lllllcf/APMC-STPM-for-SCR/figure-data/houlai/formatlab.png

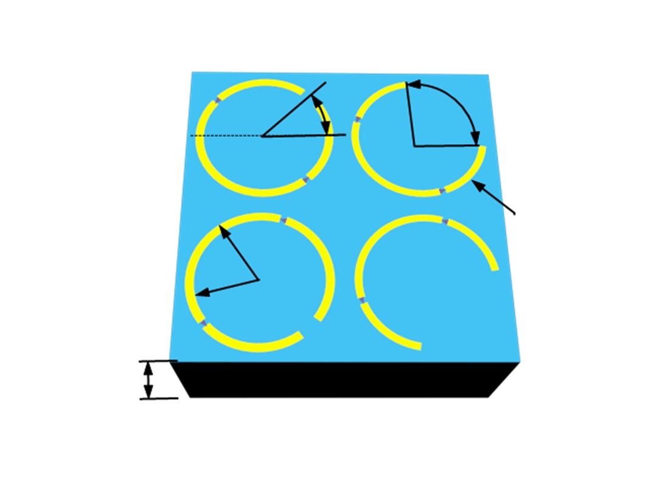
figure-data/houlai/formatlab.png
