lllllcf/APMC-STPM-for-SCR/figure-data/houlai/new.jpg

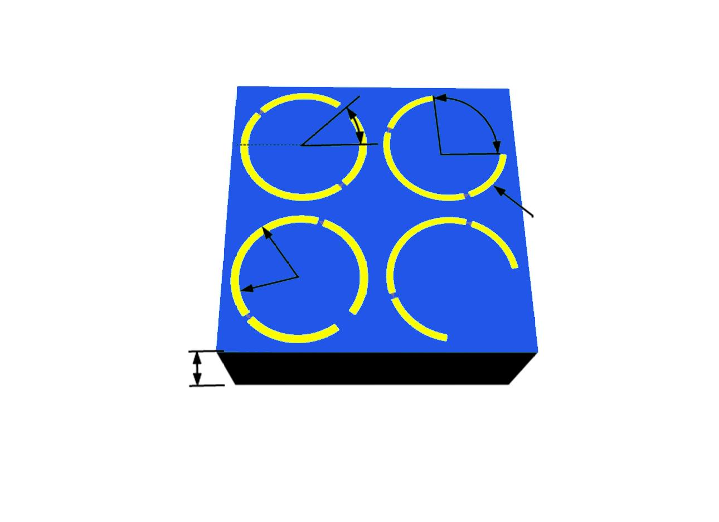
figure-data/houlai/new.jpg
