lllllcf/APMC-STPM-for-SCR/figure-data/houlai/untitled.jpg

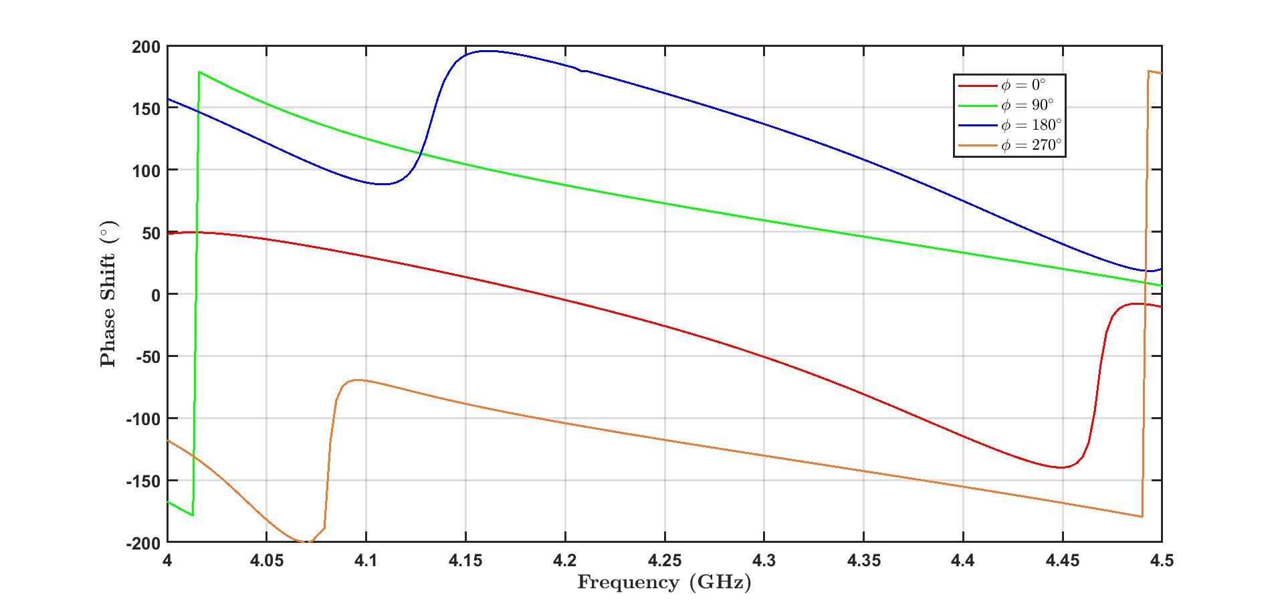
figure-data/houlai/untitled.jpg
