lllllcf/APMC-STPM-for-SCR/STPM/TMPM_figure/3D_Res/a.png

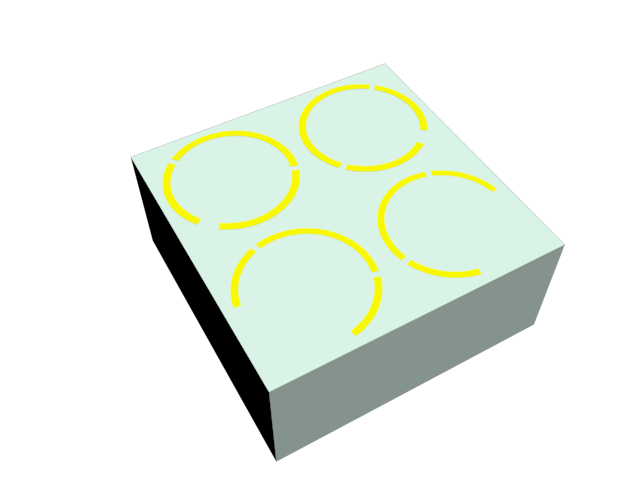
STPM/TMPM_figure/3D_Res/a.png
