lllllcf/APMC-STPM-for-SCR/STPM/TMPM_figure/3D_Res/st_se_1.png

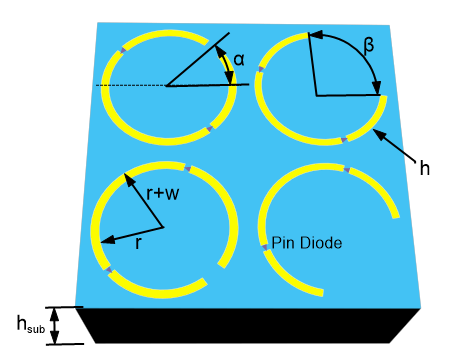
STPM/TMPM_figure/3D_Res/st_se_1.png
