lllllcf/APMC-STPM-for-SCR/STPM/TMPM_figure/new概念图/new_TMPM_line.png

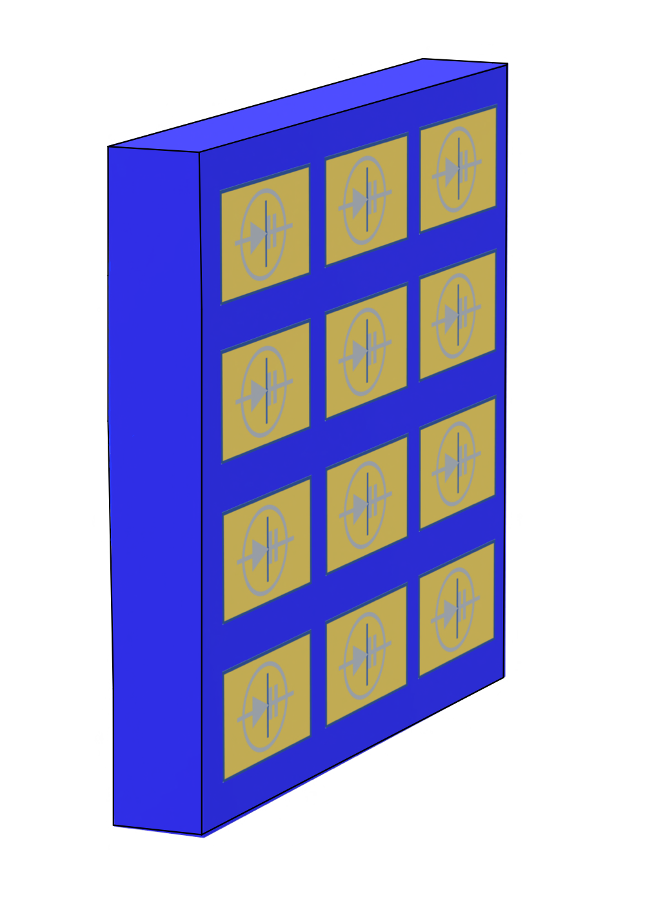
STPM/TMPM_figure/new概念图/new_TMPM_line.png
