lllllcf/APMC-STPM-for-SCR/STPM/TMPM_figure/new概念图/new_TMPM_pureBlue.png

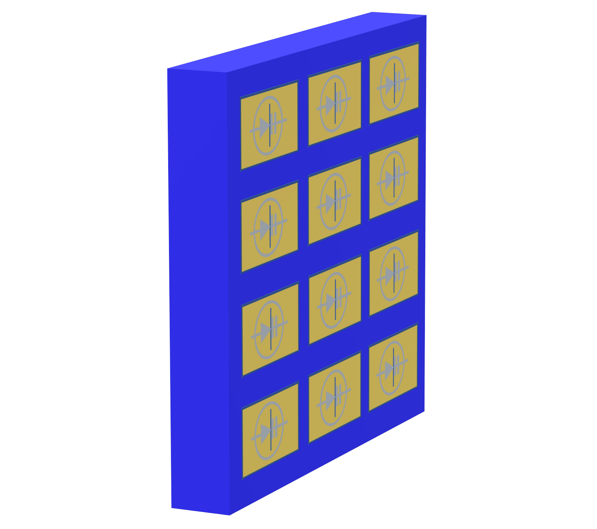
STPM/TMPM_figure/new概念图/new_TMPM_pureBlue.png
