lllllcf/APMC-STPM-for-SCR/STPM/TMPM_figure/概念图/final.png

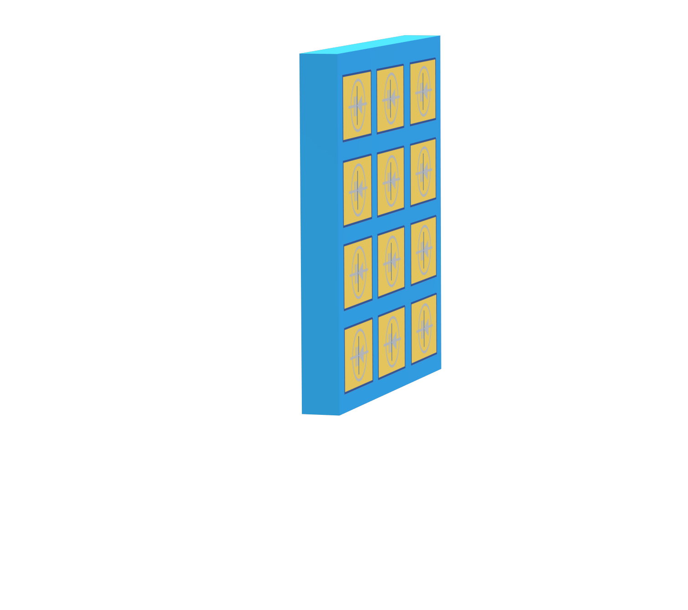
STPM/TMPM_figure/概念图/final.png
