lllllcf/APMC-STPM-for-SCR/STPM/TMPM_figure/概念图最终稿/lessb2.png

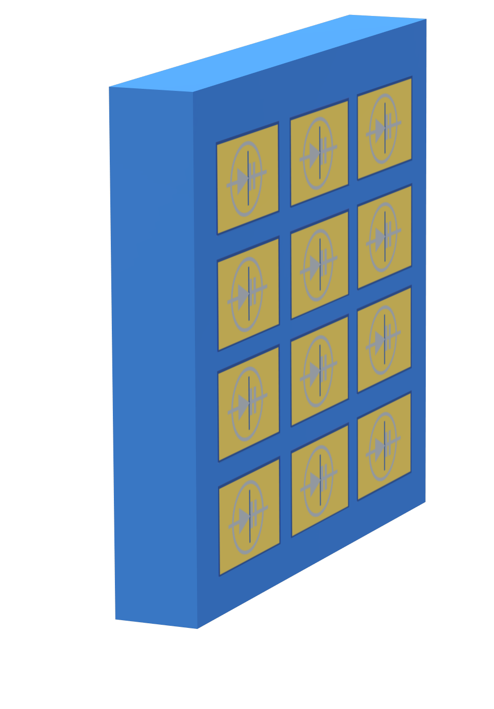
STPM/TMPM_figure/概念图最终稿/lessb2.png
