lllllcf/APMC-STPM-for-SCR/STPM/老师改了之后/jg.png

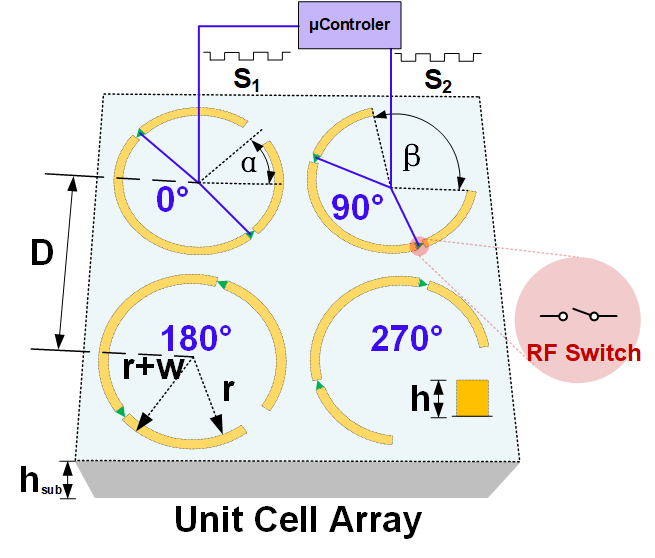
STPM/老师改了之后/jg.png
