lllllcf/APMC-STPM-for-SCR/STPM/TMPM_figure/概念图/TMPM概念图test.png

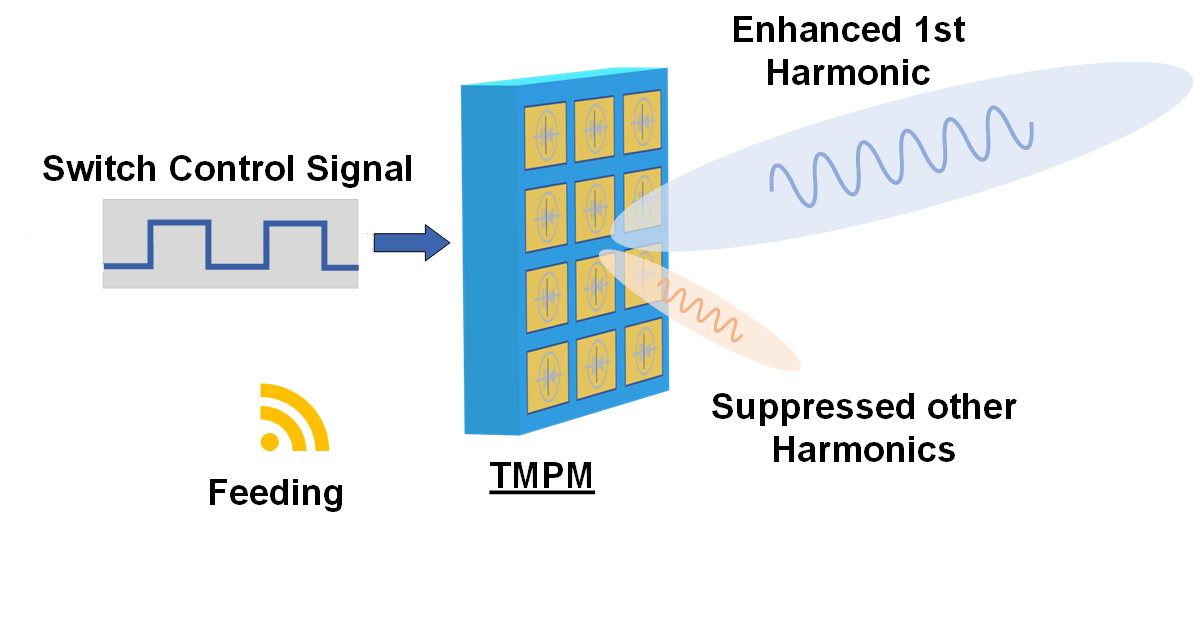
STPM/TMPM_figure/概念图/TMPM概念图test.png
