lllllcf/APMC-STPM-for-SCR/STPM/TMPM_figure/概念图/TMPM概念图final.pdf

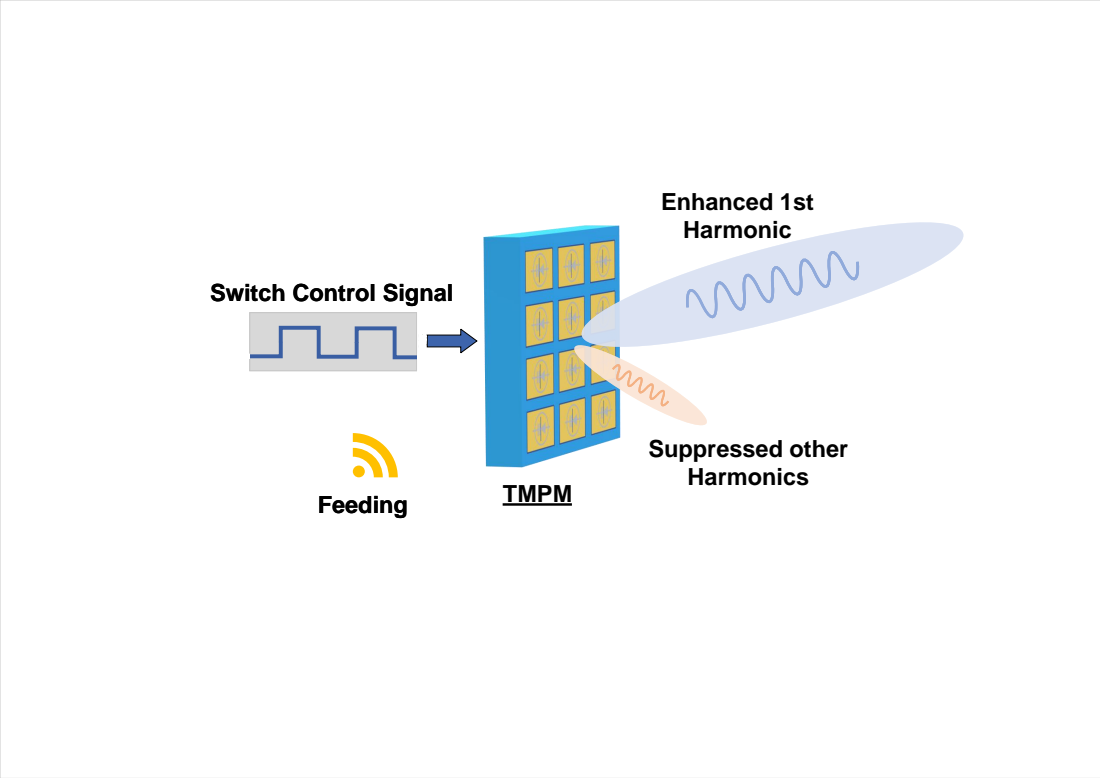
[picture p60: page 1]
TMPM; Suppressed other Harmonics; Enhanced 1st Harmonic; Feeding

Switch Control Signal
