lllllcf/APMC-STPM-for-SCR/STPM/TMPM_figure/结构图beta/jg.pdf

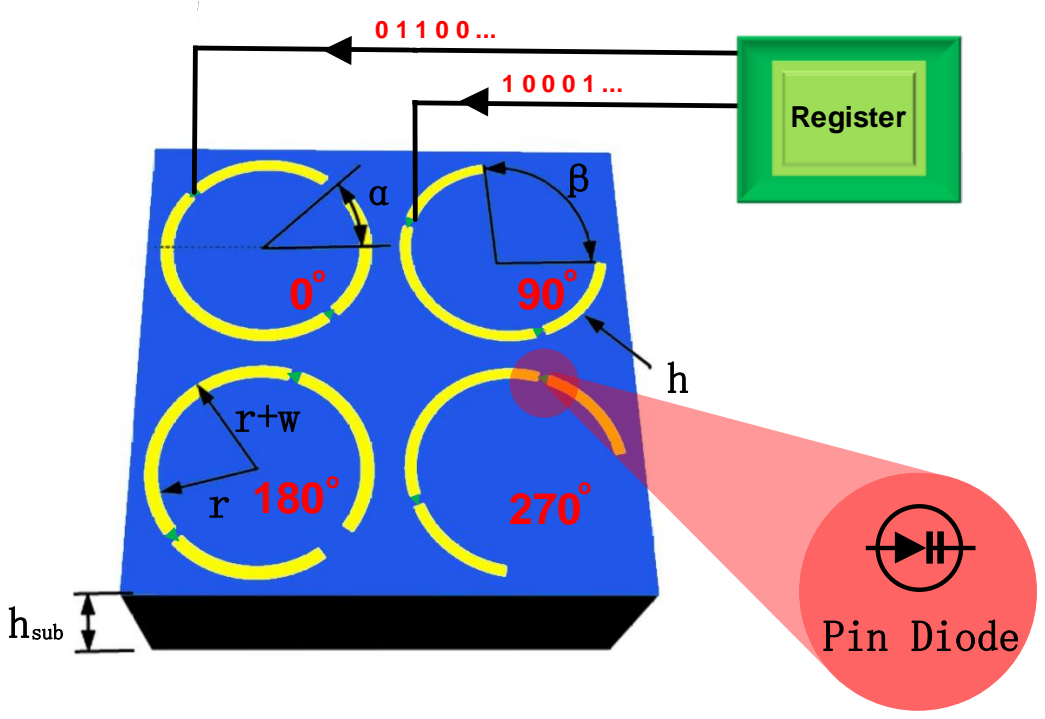
[picture p61: page 1]
hsub; Pin Diode; Register
