lllllcf/APMC-STPM-for-SCR/STPM/TMPM_figure/概念图最终稿/gnt.pdf

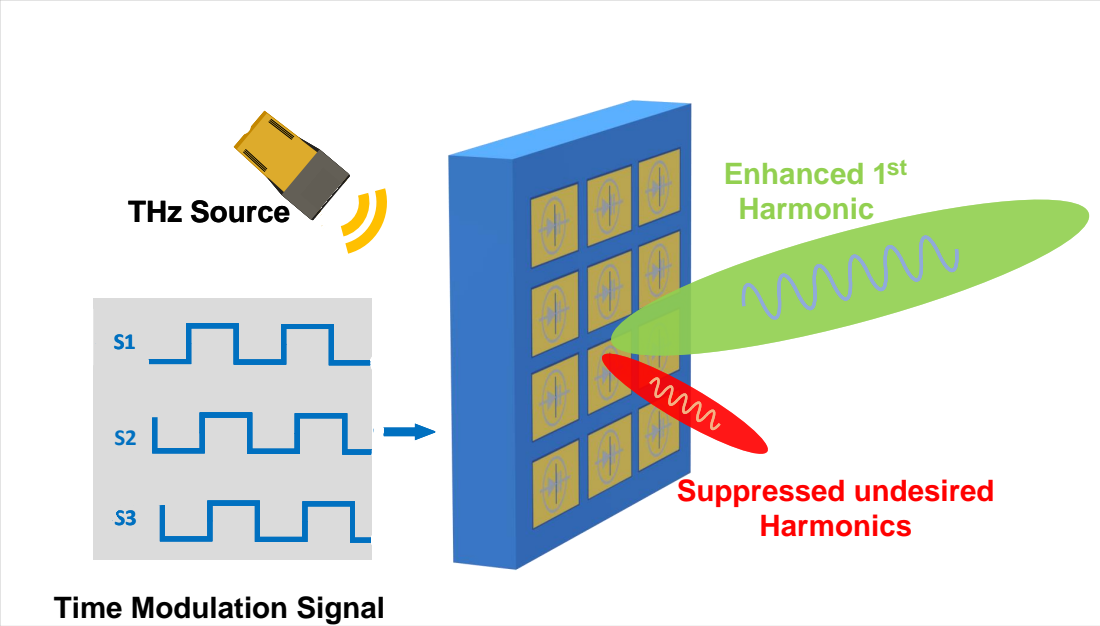
[picture p63: page 1]
Suppressed undesired Harmonics; Enhanced 1 Harmonic; THz Source

Time Modulation Signal
